lixibert/HB-DIS-EP-42/Images/IMG_20201109_173543.jpg

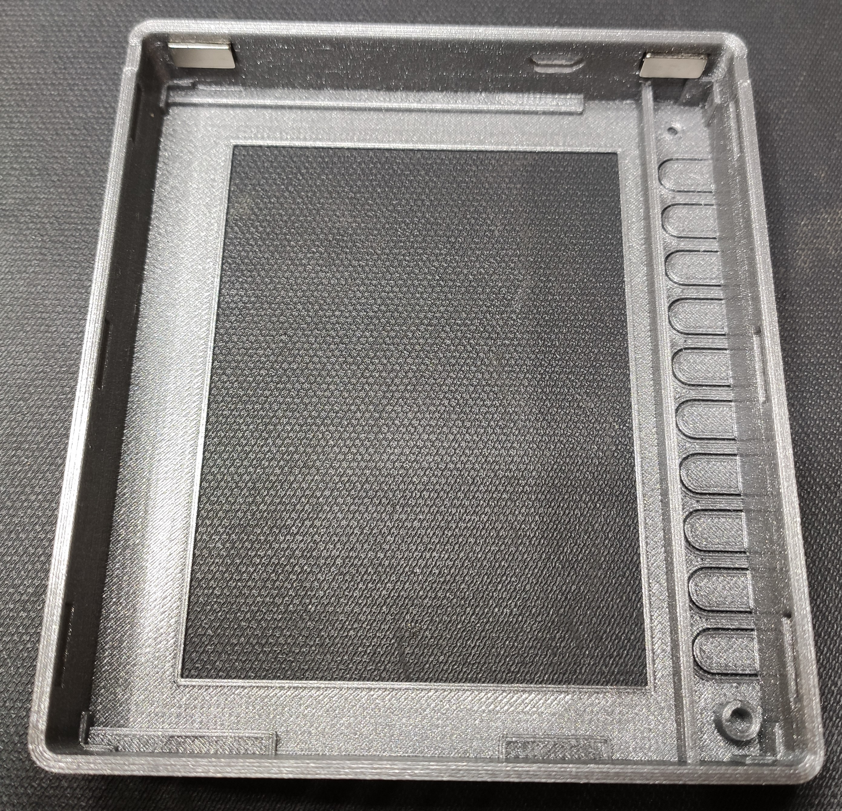
Images/IMG_20201109_173543.jpg
