lixibert/HB-DIS-EP-42/Images/IMG_20201116_160037.jpg

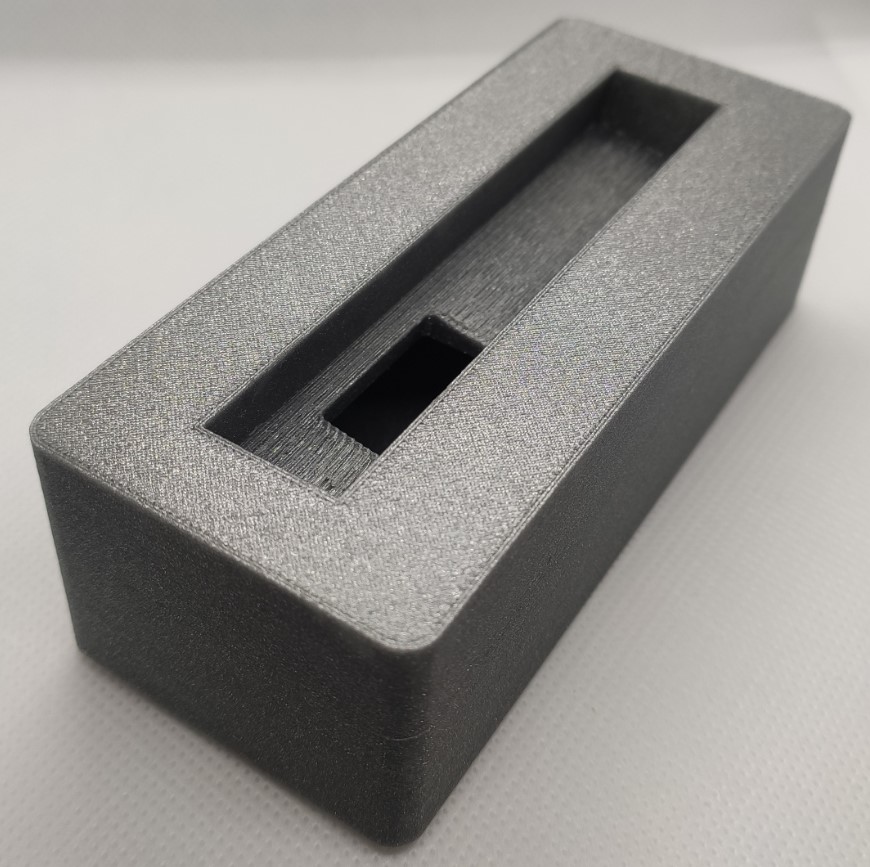
Images/IMG_20201116_160037.jpg
