lixibert/HB-DIS-EP-42/Images/IMG_20201116_160257.jpg

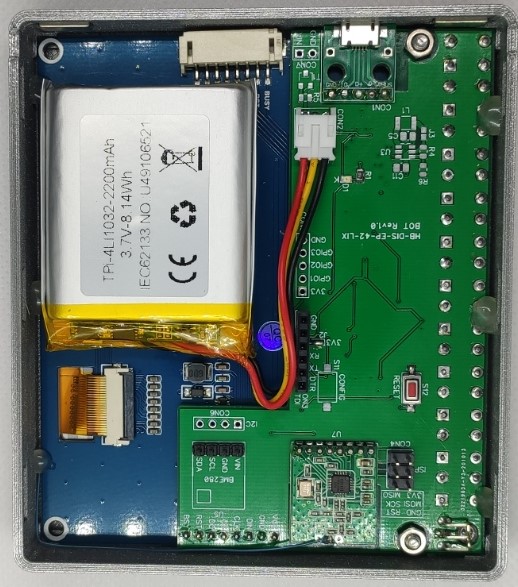
Images/IMG_20201116_160257.jpg
