lixibert/HB-DIS-EP-42/Images/IMG_20201116_160425.jpg

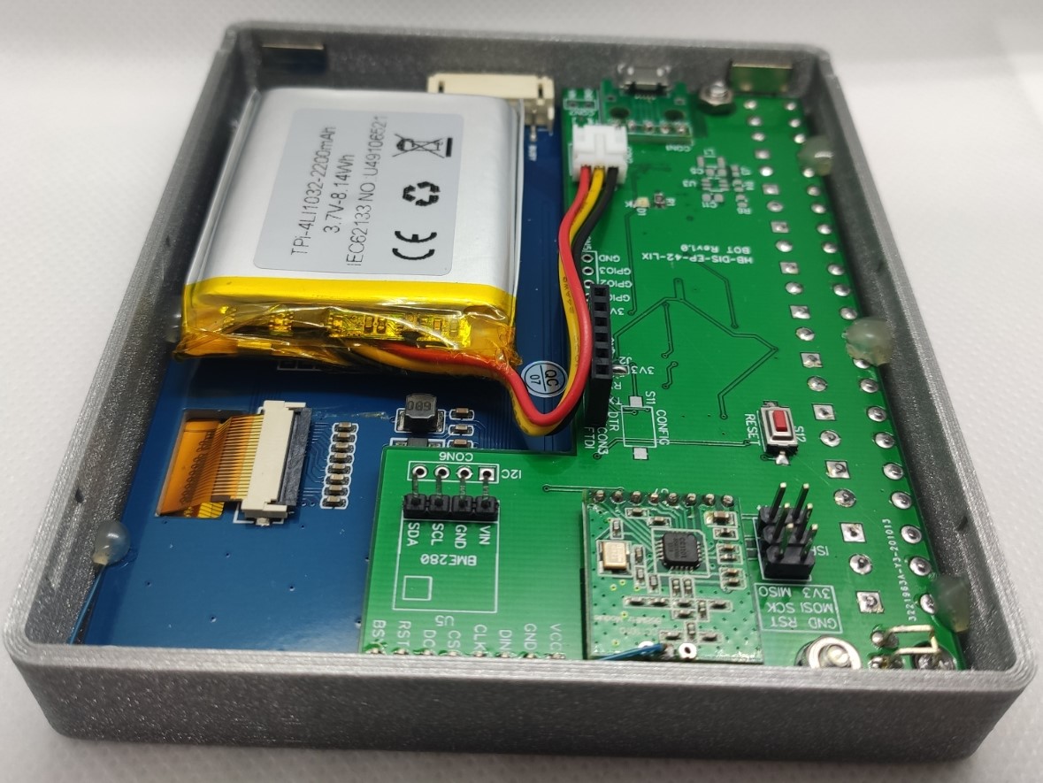
Images/IMG_20201116_160425.jpg
