lixibert/HB-DIS-EP-42/Images/IMG_20201116_160708_1.jpg

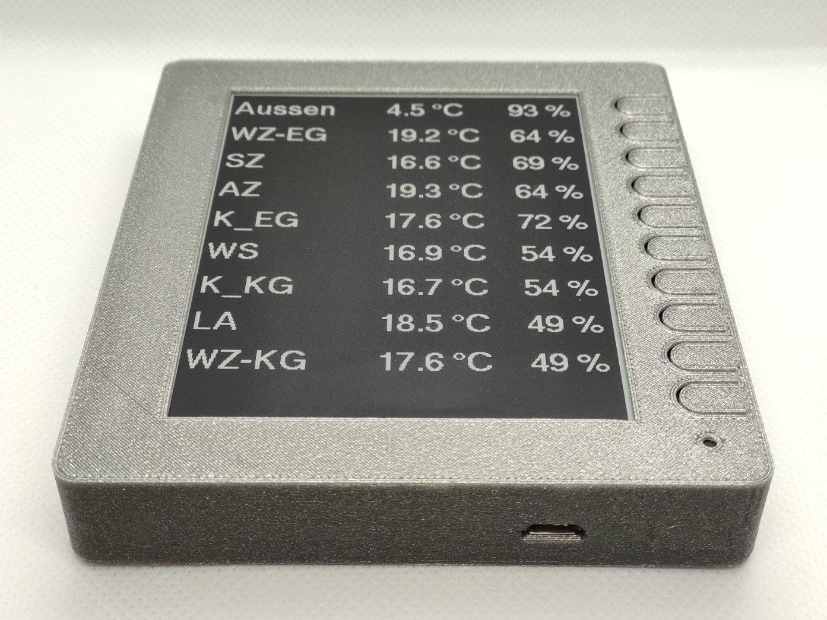
Images/IMG_20201116_160708_1.jpg
