lixibert/HB-DIS-EP-42/Images/IMG_20201121_221835.jpg

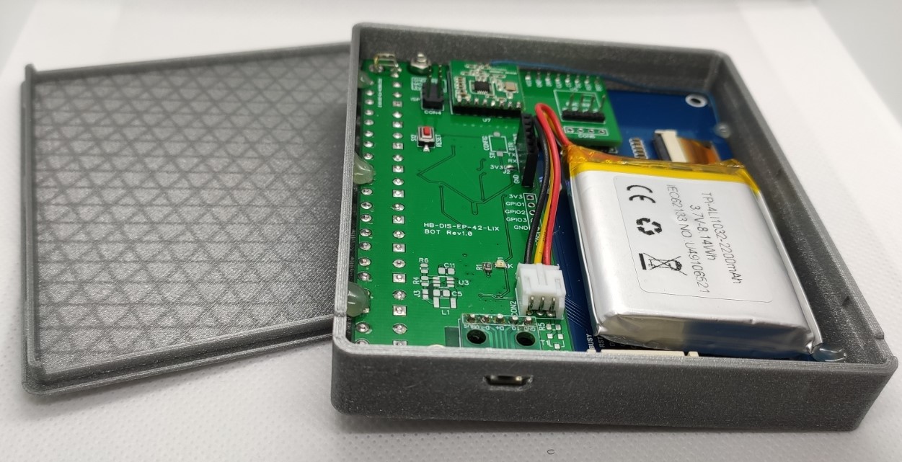
Images/IMG_20201121_221835.jpg
